Elecrow-RD/LoRaWAN-LR1262-Development-Board-Integrated-RP2040-with-1.8-LCD/example/arduino/Lora_RA-08H_Development_Board_Sample_Code/Lorawan/Sample_Code/RA_08H/RA_08H.ino

void setup() {
  // put your setup code here, to run once:
  Serial.begin(9600);
  Serial2.setRX(5);
  Serial2.setTX(4);
  Serial2.begin(9600);
}

void loop() {
  if (Serial.available())
  {
    Serial2.write(Serial.read());
  }

  if (Serial2.available())
  {
    Serial.write(Serial2.read());
  }
}
