Elecrow-RD/LoRaWAN-LR1262-Development-Board-Integrated-RP2040-with-1.8-LCD/example/arduino/Lora_RA-08H_Development_Board_Sample_Code/Lorawan/Sample_Code/buzzer/buzzer.ino

 #define NOTE_D0 -1
 #define NOTE_DL1 261
 #define NOTE_DL2 293
 #define NOTE_DL3 311
 #define NOTE_DL4 349
 #define NOTE_DL5 391
 #define NOTE_DL6 440
 #define NOTE_DL7 493
 
 #define NOTE_D1 523
 #define NOTE_D2 587
 #define NOTE_D3 659
 #define NOTE_D4 698
 #define NOTE_D5 783
 #define NOTE_D6 880
 #define NOTE_D7 987
 
 #define NOTE_DH1 1046
 #define NOTE_DH2 1174
 #define NOTE_DH3 1318
 #define NOTE_DH4 1396
 #define NOTE_DH5 1567
 #define NOTE_DH6 1760
 #define NOTE_DH7 1975
 
 #define WHOLE 1
 #define HALF 0.5
 #define QUARTER 0.25
 #define EIGHTH 0.25
 #define SIXTEENTH 0.625

 int tune[] =
 {
   NOTE_DH1, NOTE_D6, NOTE_D5, NOTE_D6, NOTE_D0,
   NOTE_DH1, NOTE_D6, NOTE_D5, NOTE_DH1, NOTE_D6, NOTE_D0, NOTE_D6,
   NOTE_D6, NOTE_D6, NOTE_D5, NOTE_D6, NOTE_D0, NOTE_D6,
   NOTE_DH1, NOTE_D6, NOTE_D5, NOTE_DH1, NOTE_D6, NOTE_D0,
 
   NOTE_D1, NOTE_D1, NOTE_D3,
   NOTE_D1, NOTE_D1, NOTE_D3, NOTE_D0,
   NOTE_D6, NOTE_D6, NOTE_D6, NOTE_D5, NOTE_D6,
   NOTE_D5, NOTE_D1, NOTE_D3, NOTE_D0,
   NOTE_DH1, NOTE_D6, NOTE_D6, NOTE_D5, NOTE_D6,
   NOTE_D5, NOTE_D1, NOTE_D2, NOTE_D0,
   NOTE_D7, NOTE_D7, NOTE_D5, NOTE_D3,
   NOTE_D5,
   NOTE_DH1, NOTE_D0, NOTE_D6, NOTE_D6, NOTE_D5, NOTE_D5, NOTE_D6, NOTE_D6,
   NOTE_D0, NOTE_D5, NOTE_D1, NOTE_D3, NOTE_D0,
   NOTE_DH1, NOTE_D0, NOTE_D6, NOTE_D6, NOTE_D5, NOTE_D5, NOTE_D6, NOTE_D6,
   NOTE_D0, NOTE_D5, NOTE_D1, NOTE_D2, NOTE_D0,
   NOTE_D3, NOTE_D3, NOTE_D1, NOTE_DL6,
   NOTE_D1,
   NOTE_D3, NOTE_D5, NOTE_D6, NOTE_D6,
   NOTE_D3, NOTE_D5, NOTE_D6, NOTE_D6,
   NOTE_DH1, NOTE_D0, NOTE_D7, NOTE_D5,
   NOTE_D6,
 };

 float duration[] =
 {
   1, 1, 0.5, 0.5, 1,
   0.5, 0.5, 0.5, 0.5, 1, 0.5, 0.5,
   0.5, 1, 0.5, 1, 0.5, 0.5,
   0.5, 0.5, 0.5, 0.5, 1, 1,
 
   1, 1, 1 + 1,
   0.5, 1, 1 + 0.5, 1,
   1, 1, 0.5, 0.5, 1,
   0.5, 1, 1 + 0.5, 1,
   0.5, 0.5, 0.5, 0.5, 1 + 1,
   0.5, 1, 1 + 0.5, 1,
   1 + 1, 0.5, 0.5, 1,
   1 + 1 + 1 + 1,
   0.5, 0.5, 0.5 + 0.25, 0.25, 0.5 + 0.25, 0.25, 0.5 + 0.25, 0.25,
   0.5, 1, 0.5, 1, 1,
   0.5, 0.5, 0.5 + 0.25, 0.25, 0.5 + 0.25, 0.25, 0.5 + 0.25, 0.25,
   0.5, 1, 0.5, 1, 1,
   1 + 1, 0.5, 0.5, 1,
   1 + 1 + 1 + 1,
   0.5, 1, 0.5, 1 + 1,
   0.5, 1, 0.5, 1 + 1,
   1 + 1, 0.5, 0.5, 1,
   1 + 1 + 1 + 1
 };
 int length;
 int tonePin = 28; 
 
 void setup()
 {
   pinMode(tonePin, OUTPUT); 
   length = sizeof(tune) / sizeof(tune[0]);
 }
 void loop()
 {
   for (int x = 0; x < length; x++) 
   {
     tone(tonePin, tune[x]); 
     delay(400 * duration[x]); 
     noTone(tonePin);
   }
   delay(5000);
 }                    
