Elecrow-RD/LoRaWAN-LR1262-Development-Board-Integrated-RP2040-with-1.8-LCD/example/arduino/Lora_RA-08H_Development_Board_Sample_Code/Lora/RA08H_Receive/08H_Receive.ino

void setup() {
  // put your setup code here, to run once:
  Serial.begin(9600);
  Serial2.setRX(5);
  Serial2.setTX(4);
  Serial2.begin(9600);
  Serial2.println("AT+CADDRSET=12");
  delay(1000);
  Serial2.println("AT+CTXADDRSET=13");
  delay(1000);
  Serial2.println("AT+CADDRSET=12");
  delay(1000);
  Serial2.println("AT+CTXADDRSET=13");
  delay(1000);
  Serial2.println("AT+CADDRSET=12");
  delay(1000);
  Serial2.println("AT+CTXADDRSET=13");
  delay(1000);
  Serial2.println("AT+CRXS=868100000,5,0,1,1");
  delay(1000);
}

void loop() {
  if (Serial2.available())
  {
    Serial.write(Serial2.read());
  }
}
